f-rower/Crazyflie-monopod-perching/Results/TiltAngle.xlsx

Sheet: Sheet1
L | L/l | Theta | T1 | l | m | M | g
0.01 | 0.2857142857 | 30.14778759 | 0.05625 | 0.035 | 0.004 | 0.032 | 9.8 | 0.2857142857 | 32
0.02 | 0.5714285714 | 14.54356536 | 0.05625 | 0.035 | 0.004 | 0.032 | 9.8 | 0.5714285714 | 14.3
0.03 | 0.8571428571 | 9.637306499 | 0.05625 | 0.035 | 0.004 | 0.032 | 9.8 | 0.8571428571 | 12.2
0.04 | 1.142857143 | 7.212982772 | 0.05625 | 0.035 | 0.004 | 0.032 | 9.8 | 1.142857143 | 9.1
0.05 | 1.428571429 | 5.76487839 | 0.05625 | 0.035 | 0.004 | 0.032 | 9.8 | 1.714285714 | 6.9
0.06 | 1.714285714 | 4.801581975 | 0.05625 | 0.035 | 0.004 | 0.032 | 9.8 | 2.285714286 | 6.1
0.07 | 2 | 4.114361093 | 0.05625 | 0.035 | 0.004 | 0.032 | 9.8 | 2.857142857 | 4.33
0.08 | 2.285714286 | 3.5993397 | 0.05625 | 0.035 | 0.004 | 0.032 | 9.8 | 3.428571429 | 3.9
0.09 | 2.571428571 | 3.198970878 | 0.05625 | 0.035 | 0.004 | 0.032 | 9.8
0.1 | 2.857142857 | 2.878789307 | 0.05625 | 0.035 | 0.004 | 0.032 | 9.8
0.11 | 3.142857143 | 2.616889927 | 0.05625 | 0.035 | 0.004 | 0.032 | 9.8
0.12 | 3.428571429 | 2.398682465 | 0.05625 | 0.035 | 0.004 | 0.032 | 9.8
0.13 | 3.714285714 | 2.214072695 | 0.05625 | 0.035 | 0.004 | 0.032 | 9.8 |  | 0.01
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
