f-rower/Crazyflie-monopod-perching/Results/Pictures/1cm_oscillations.png

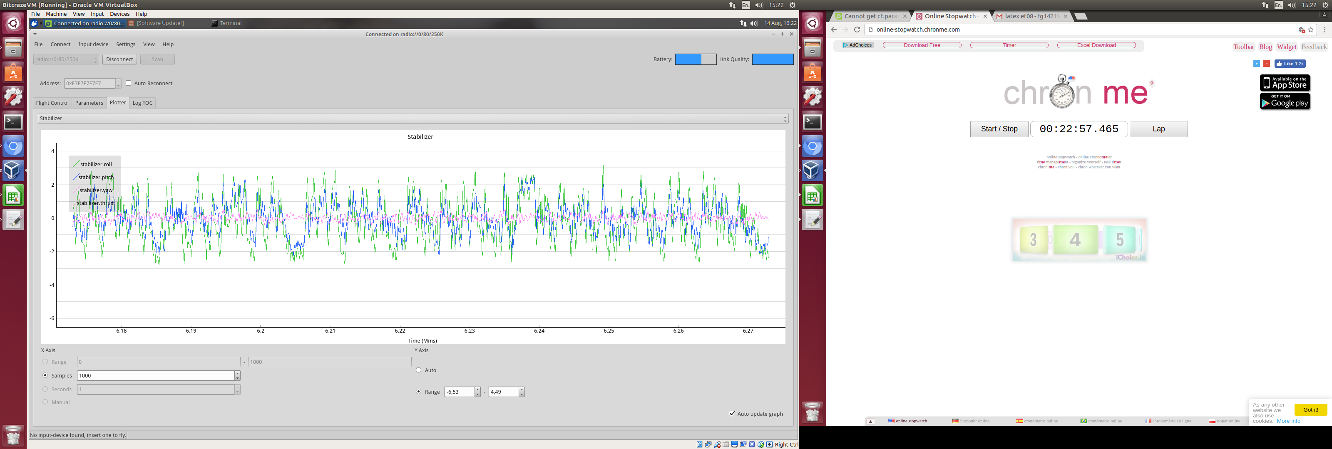
Results/Pictures/1cm_oscillations.png
