f-rower/Crazyflie-monopod-perching/Results/Pictures/2_cm_yellow_support_normal_battery.png

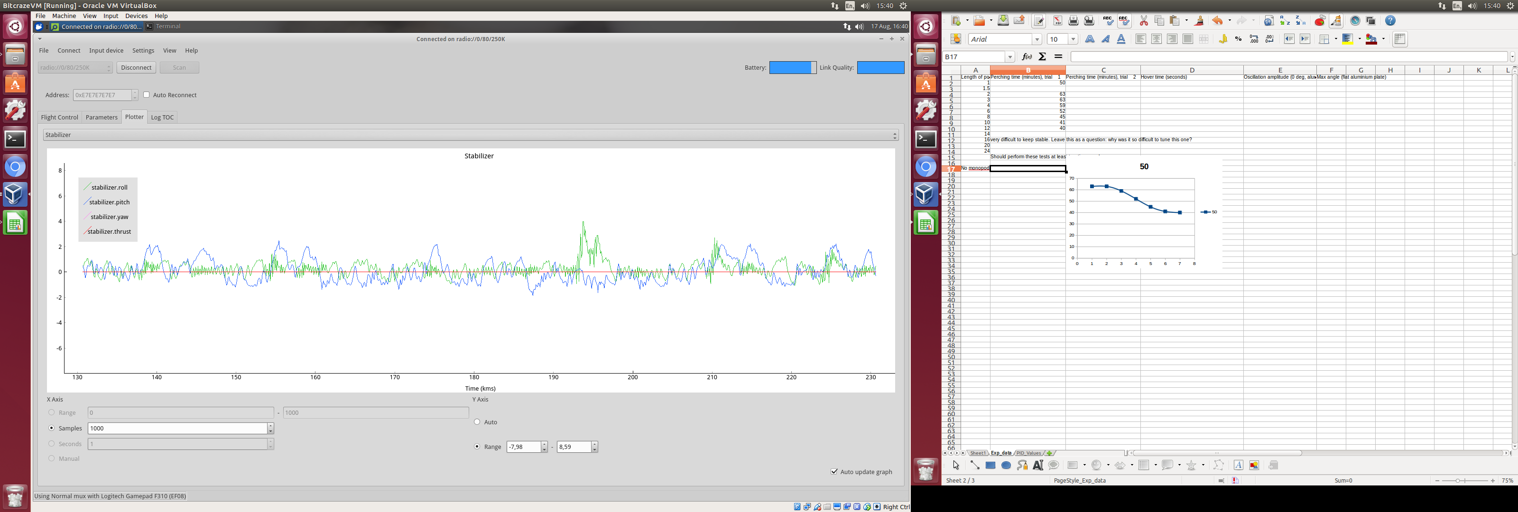
Results/Pictures/2_cm_yellow_support_normal_battery.png
