f-rower/Crazyflie-monopod-perching/Results/Pictures/2cm_pitch_1.png

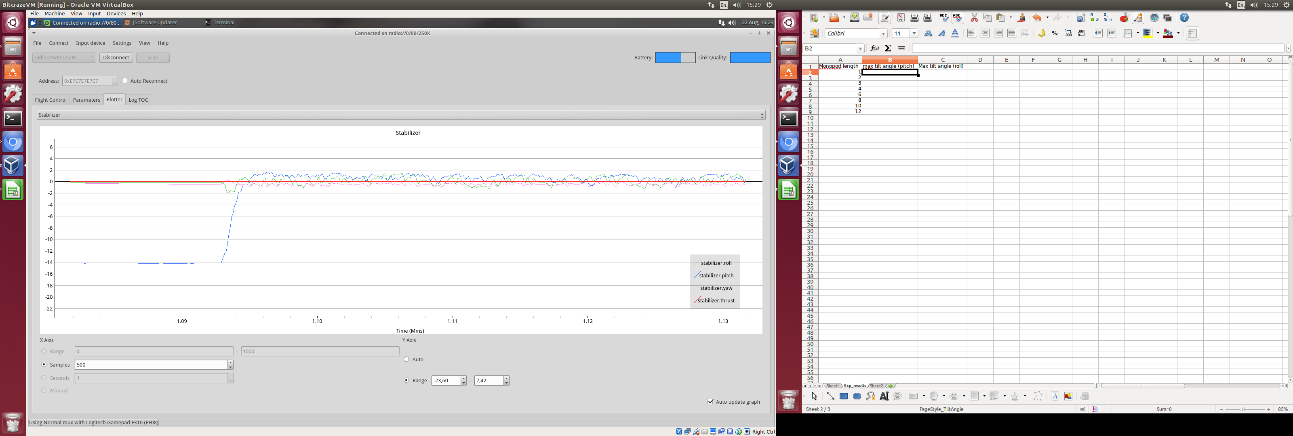
Results/Pictures/2cm_pitch_1.png
