f-rower/Crazyflie-monopod-perching/Results/Pictures/2cm_pitch_2.png

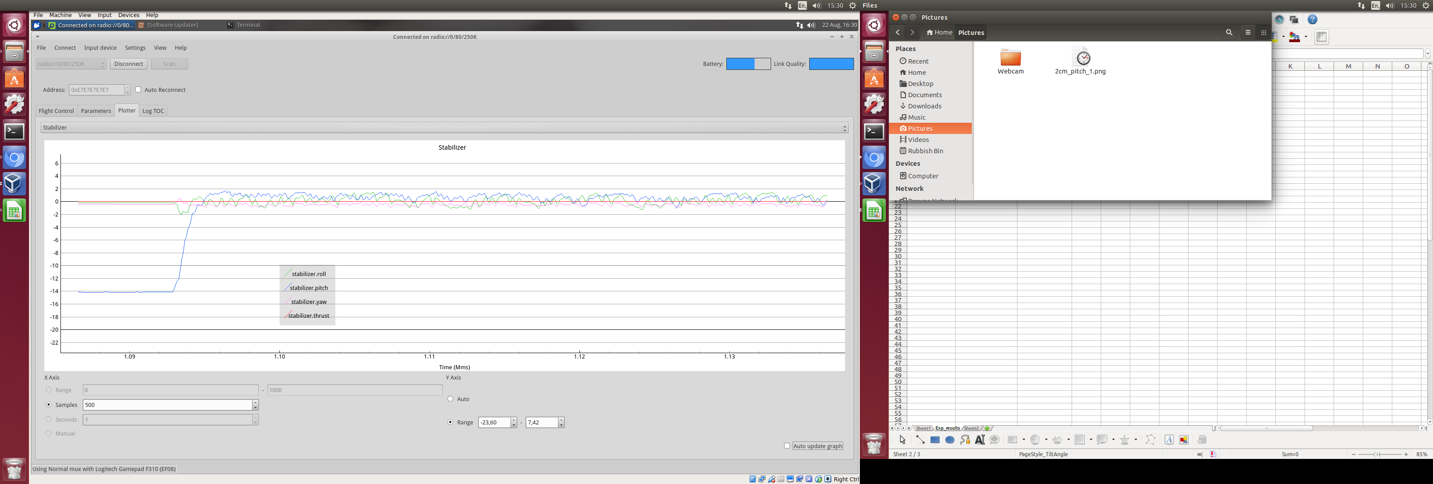
Results/Pictures/2cm_pitch_2.png
