f-rower/Crazyflie-monopod-perching/Results/Pictures/2cm_pitch_3.png

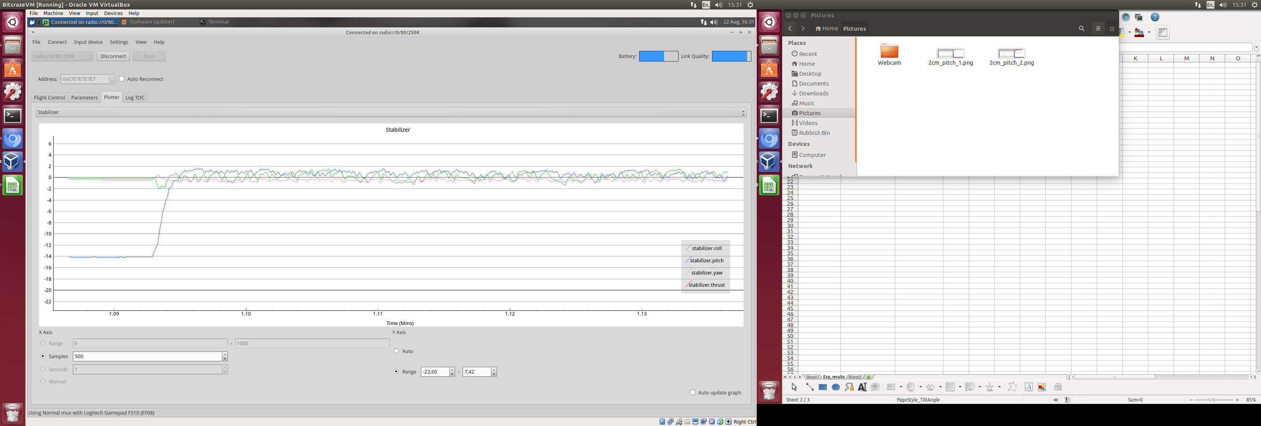
Results/Pictures/2cm_pitch_3.png
