f-rower/Crazyflie-monopod-perching/Results/Pictures/2cm_yawrate_2.png

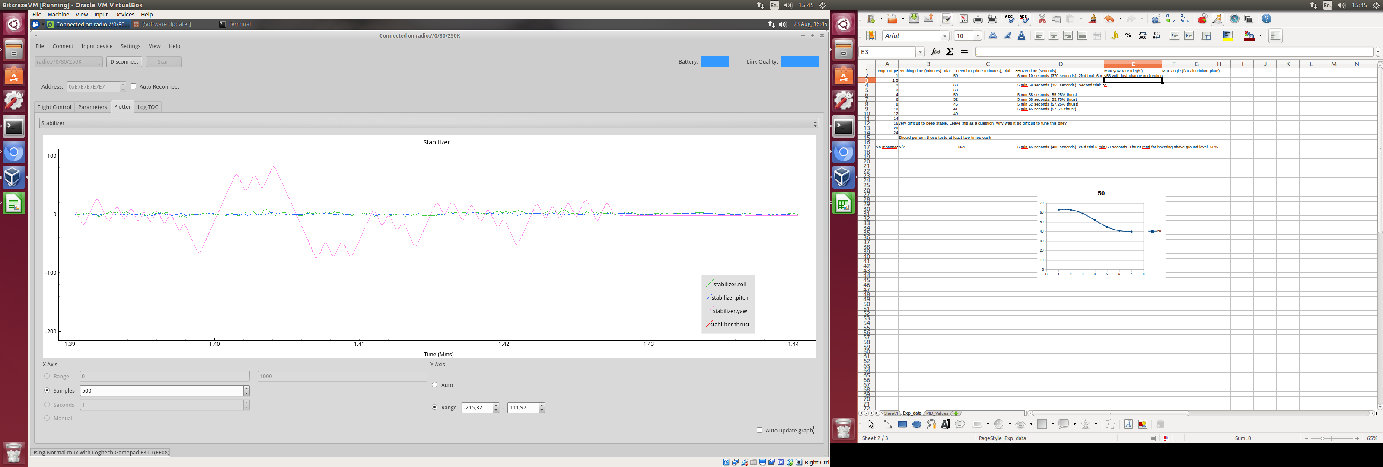
Results/Pictures/2cm_yawrate_2.png
