f-rower/Crazyflie-monopod-perching/Results/Pictures/4cm_pitch.png

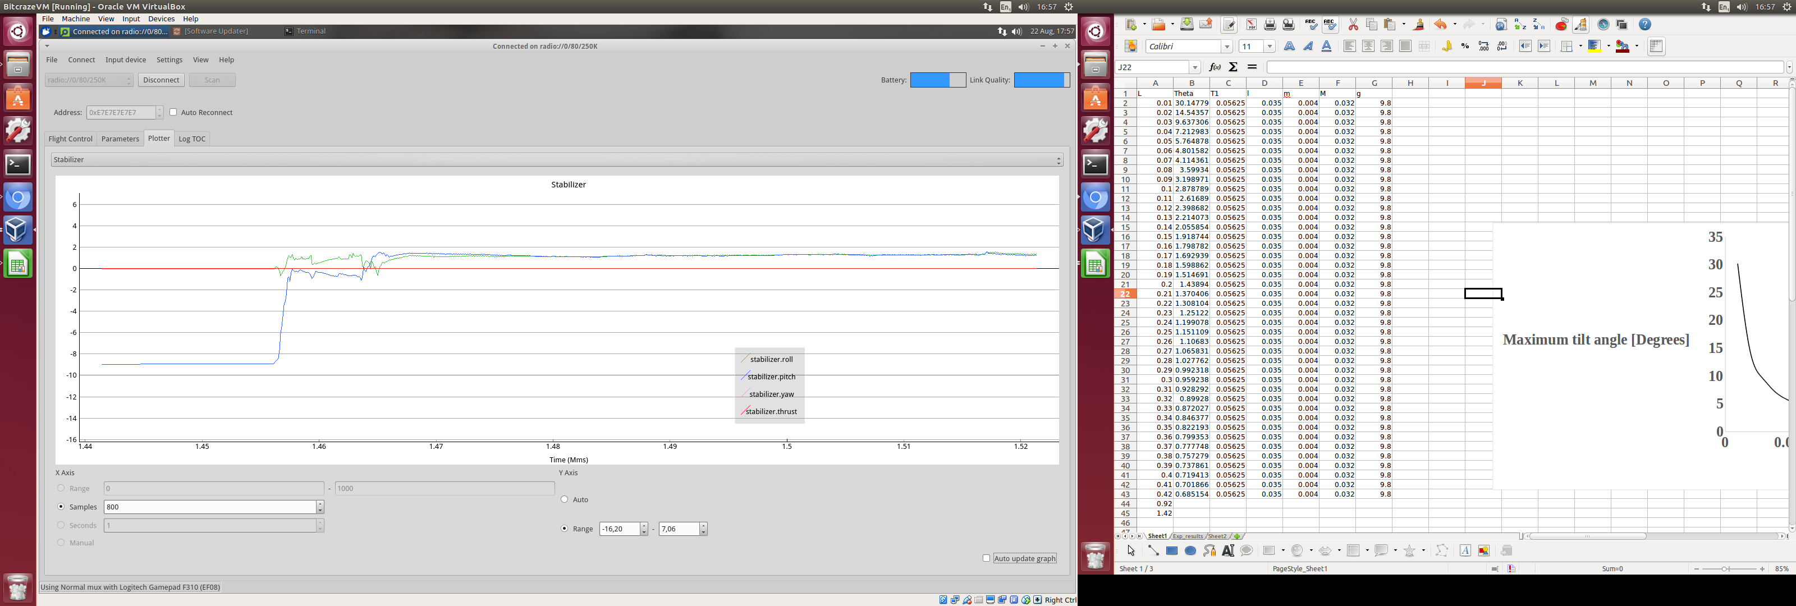
Results/Pictures/4cm_pitch.png
