f-rower/Crazyflie-monopod-perching/Results/Pictures/25_percent_base_thrust.png

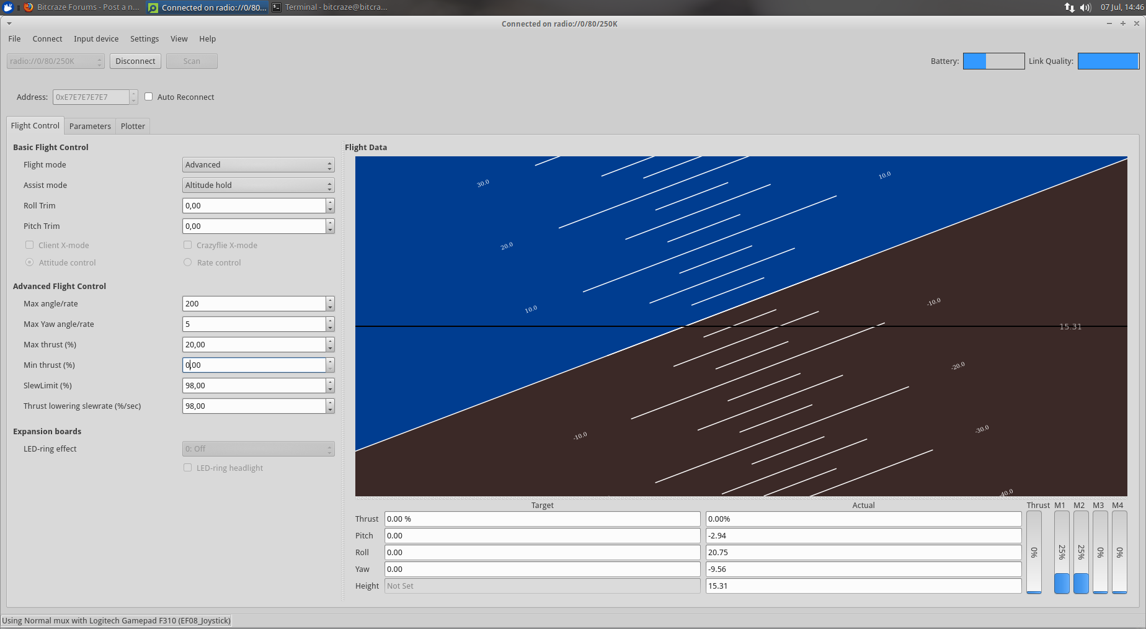
Results/Pictures/25_percent_base_thrust.png
