f-rower/Crazyflie-monopod-perching/Results/Pictures/457_goes_crazy.png

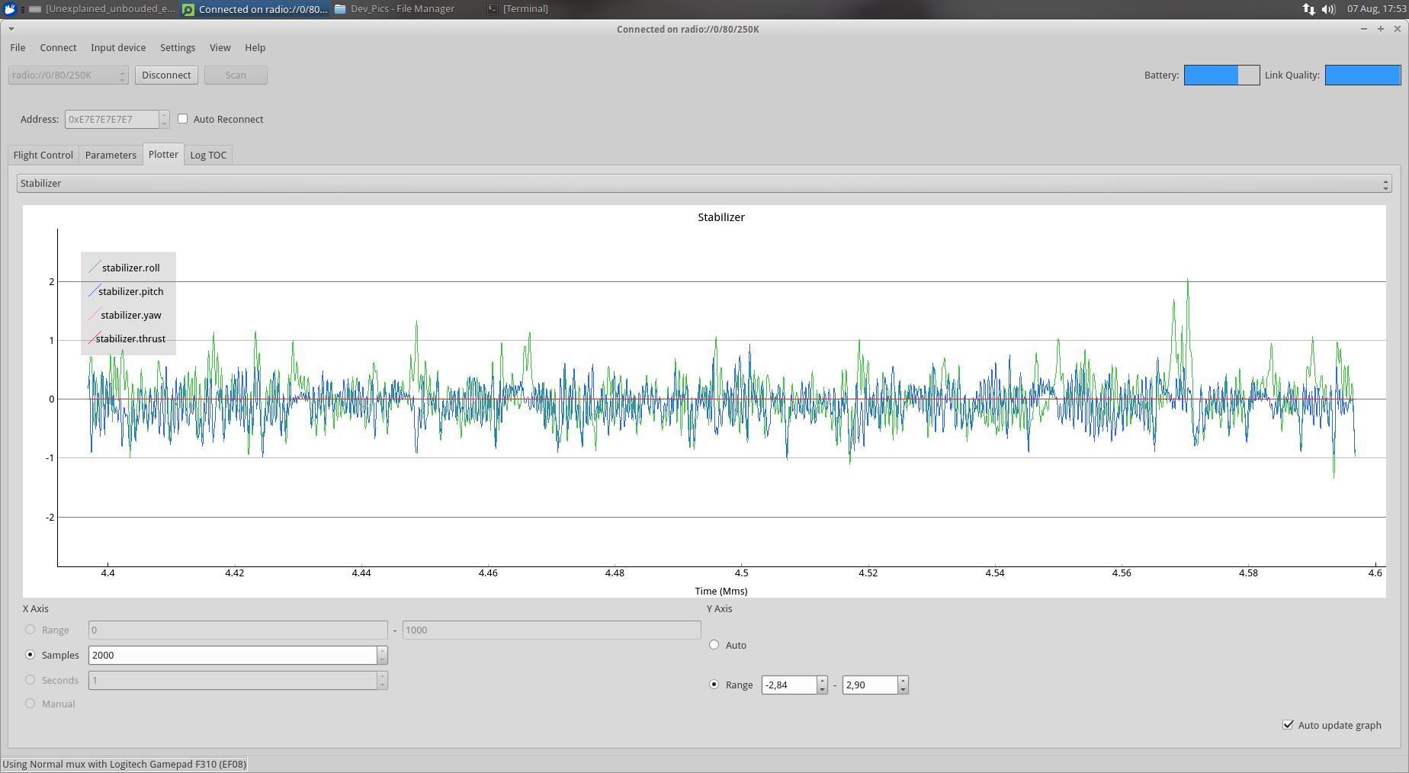
Results/Pictures/457_goes_crazy.png
