f-rower/Crazyflie-monopod-perching/Results/Pictures/2017_08_25/IMG_20170810_175333.jpg

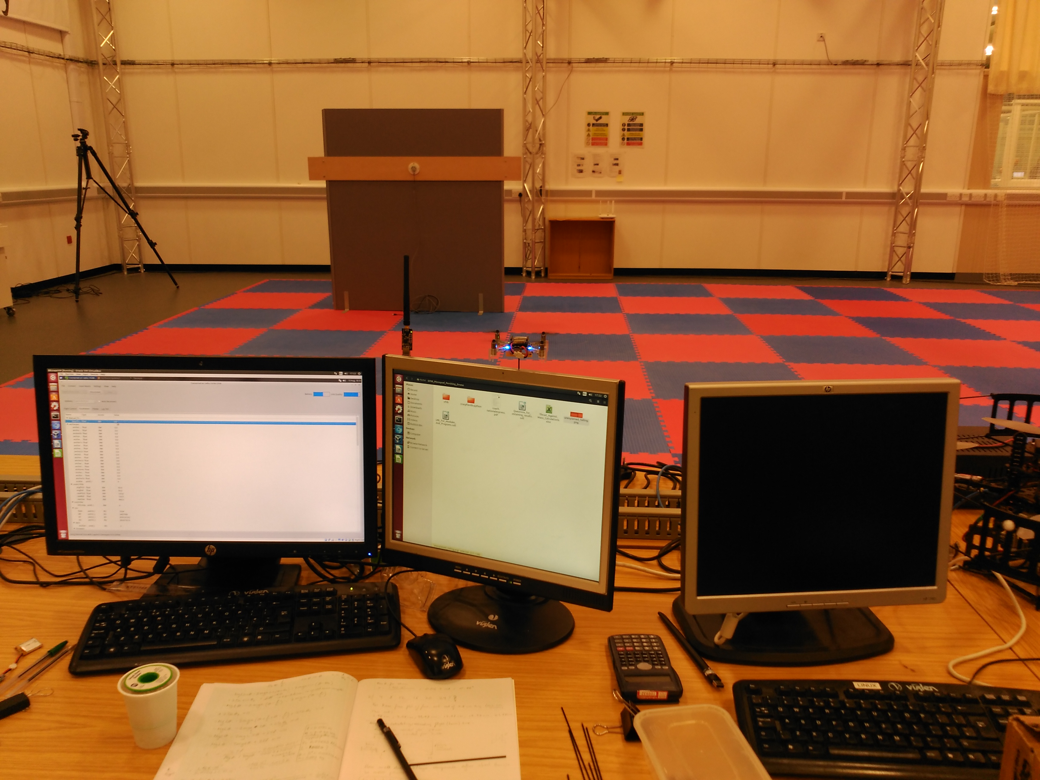
Results/Pictures/2017_08_25/IMG_20170810_175333.jpg
