f-rower/Crazyflie-monopod-perching/Results/Pictures/2017_08_25/IMG_20170825_134307.jpg

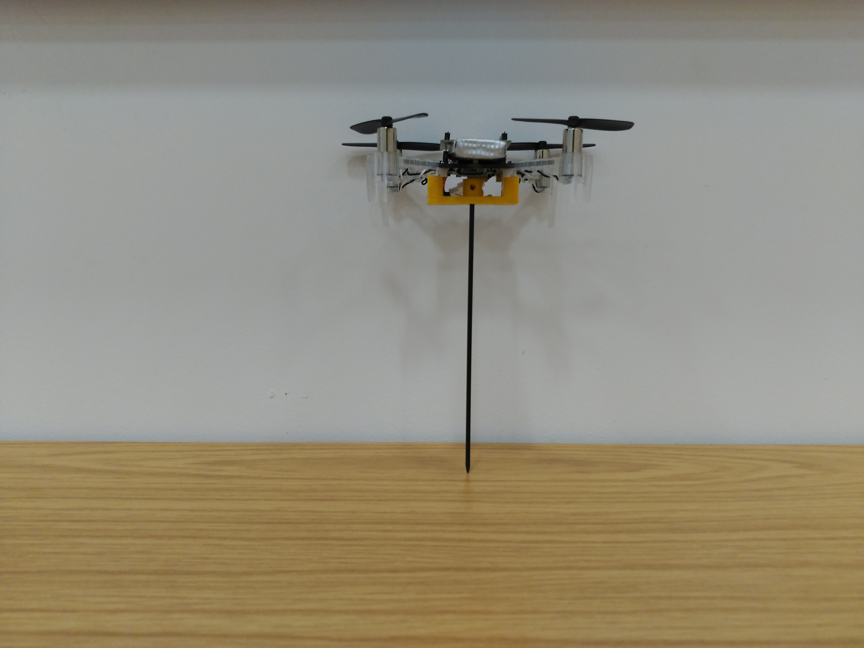
Results/Pictures/2017_08_25/IMG_20170825_134307.jpg
