f-rower/Crazyflie-monopod-perching/Results/Pictures/behaviour_when_low_battery.png

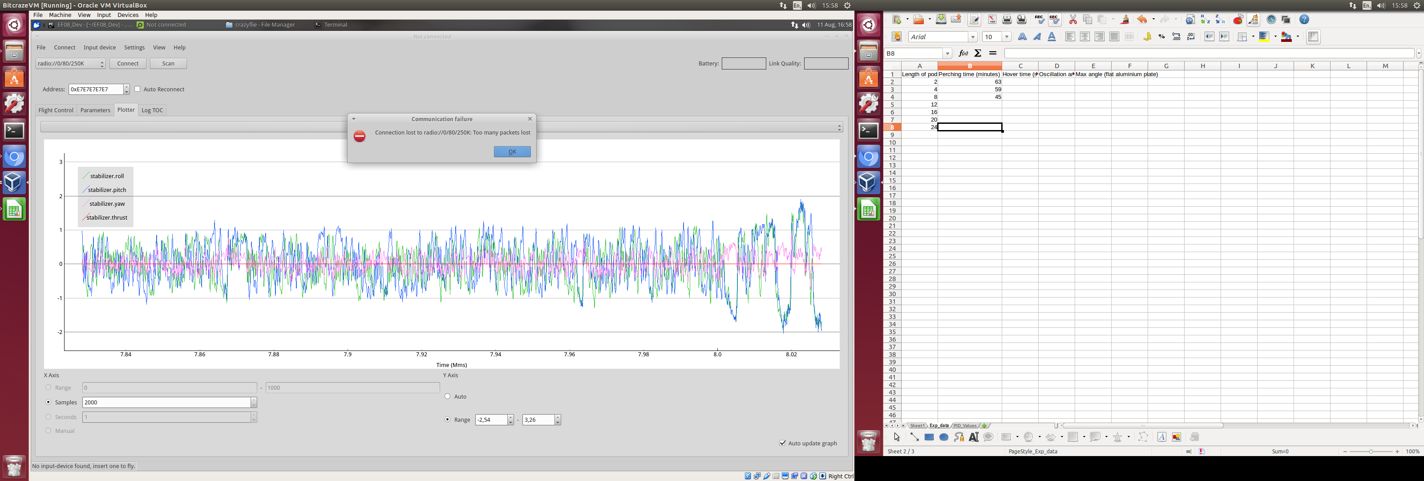
Results/Pictures/behaviour_when_low_battery.png
