f-rower/Crazyflie-monopod-perching/Results/Pictures/Motor_Voltage_end.png

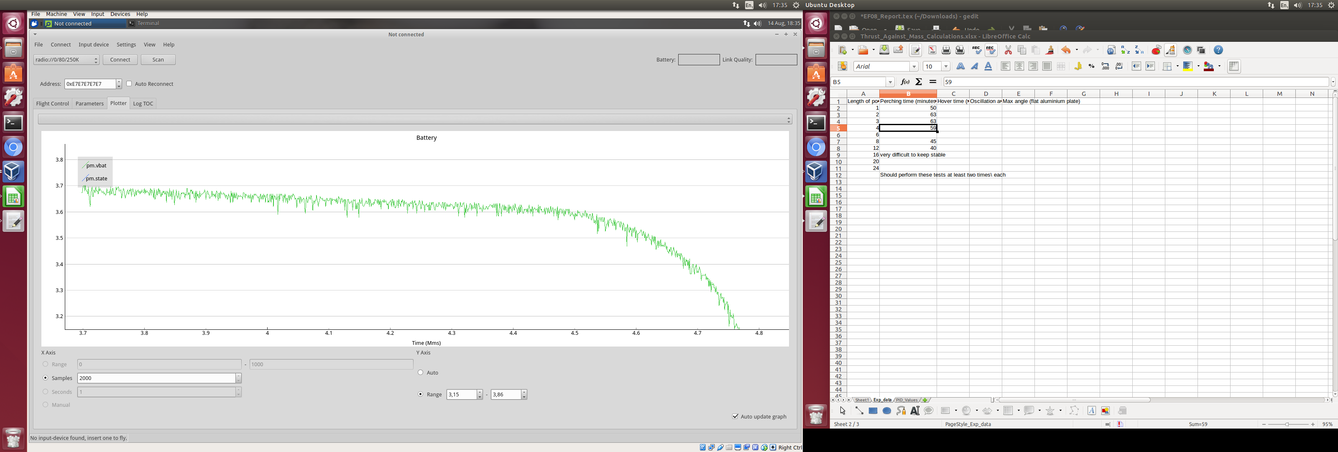
Results/Pictures/Motor_Voltage_end.png
