f-rower/Crazyflie-monopod-perching/Results/Pictures/Roll_1dof_rig_ratemode.png

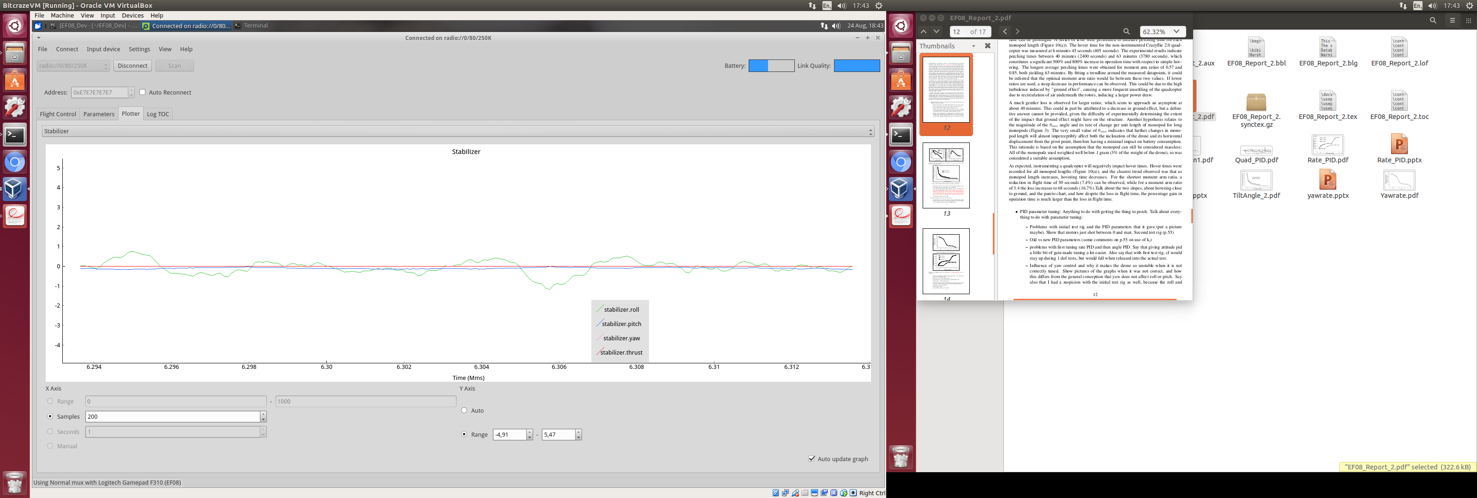
Results/Pictures/Roll_1dof_rig_ratemode.png
