f-rower/Crazyflie-monopod-perching/Results/Pictures/ROll_instability.png

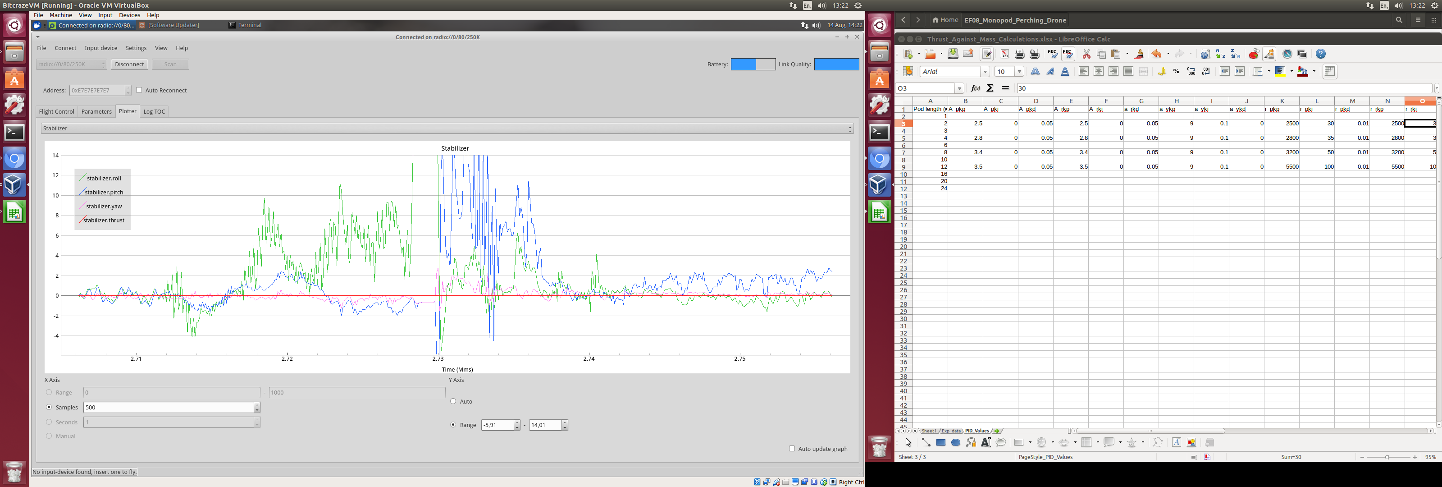
Results/Pictures/ROll_instability.png
