f-rower/Crazyflie-monopod-perching/Results/Pictures/Roll_Instability_2.png

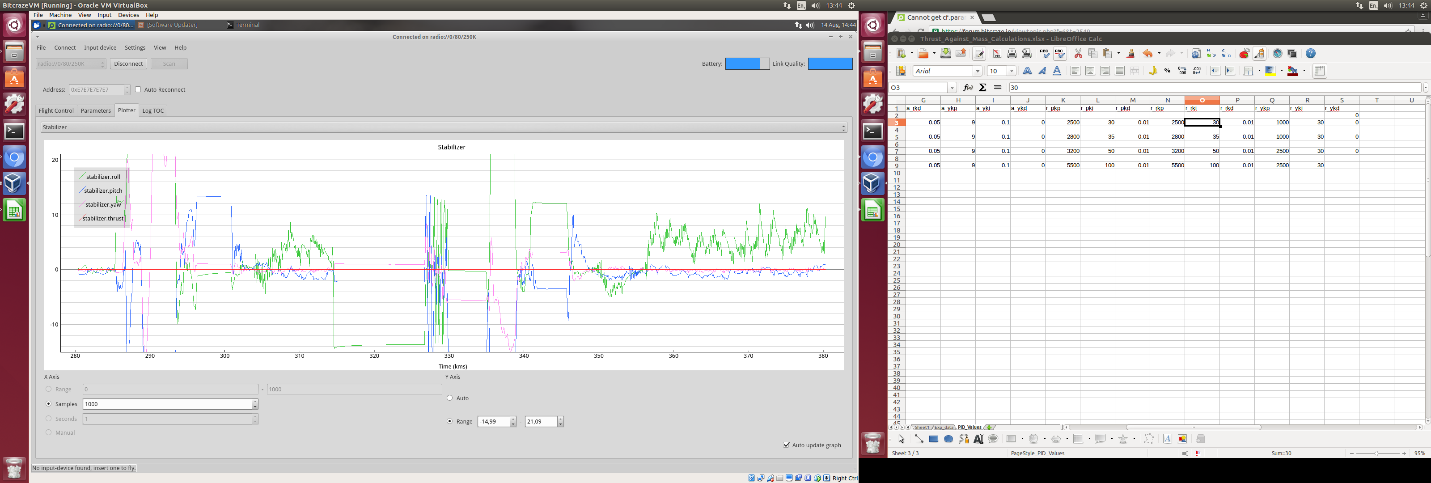
Results/Pictures/Roll_Instability_2.png
