f-rower/Crazyflie-monopod-perching/Results/Pictures/unexplained_falling.png

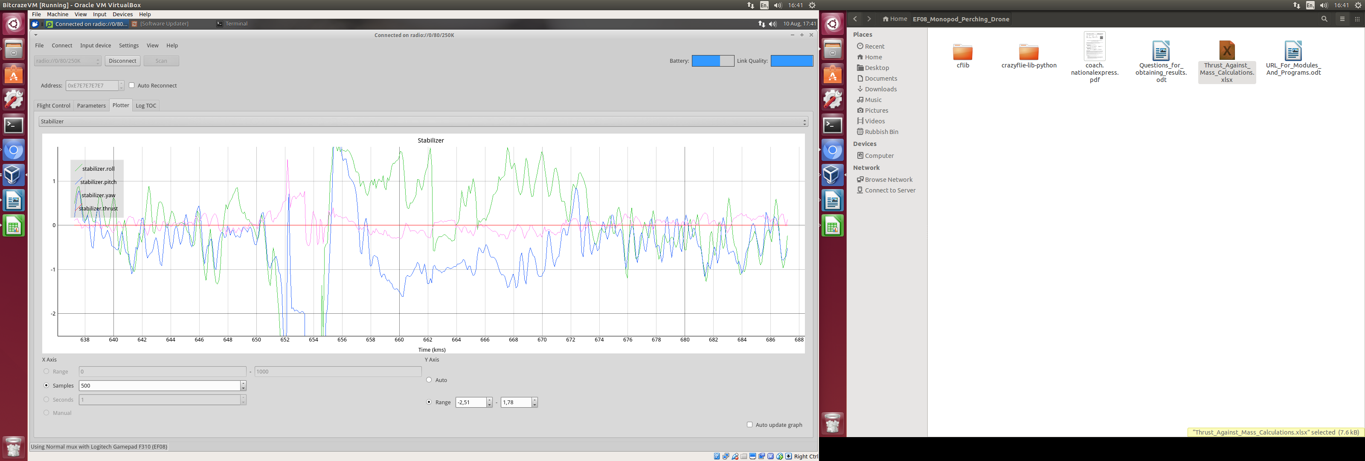
Results/Pictures/unexplained_falling.png
