f-rower/Crazyflie-monopod-perching/Results/Pictures/Unexplained_unbouded_error_growth-5.png

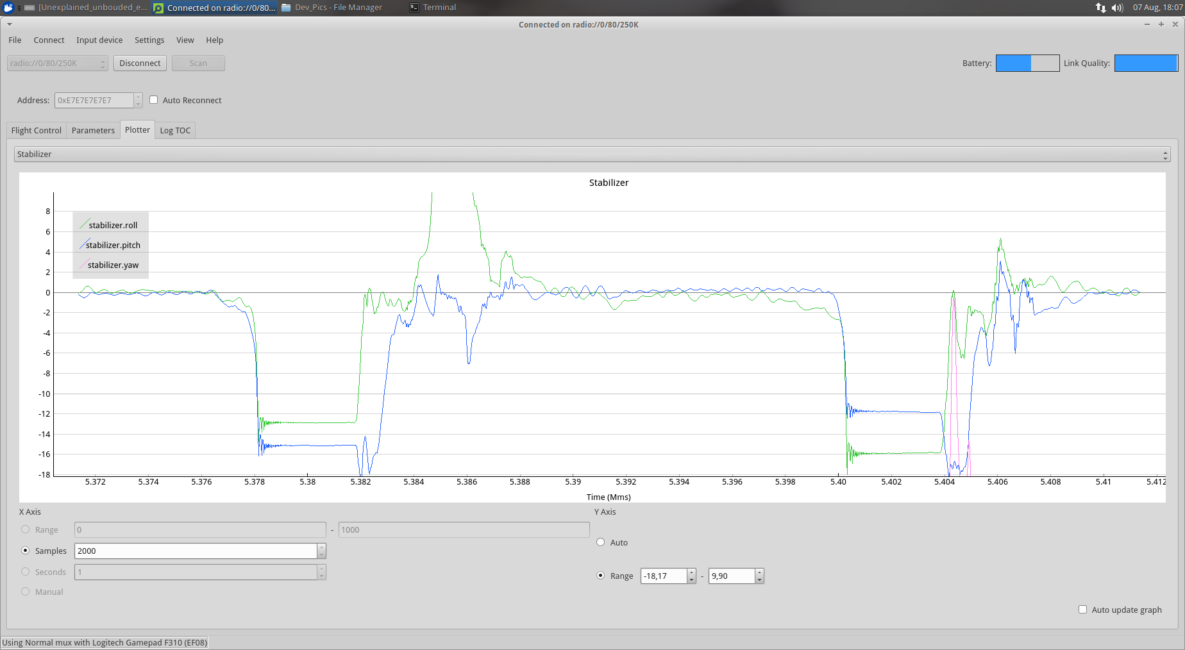
Results/Pictures/Unexplained_unbouded_error_growth-5.png
