f-rower/Crazyflie-monopod-perching/Results/Pictures/Unexplained_unbouded_error_growth.png

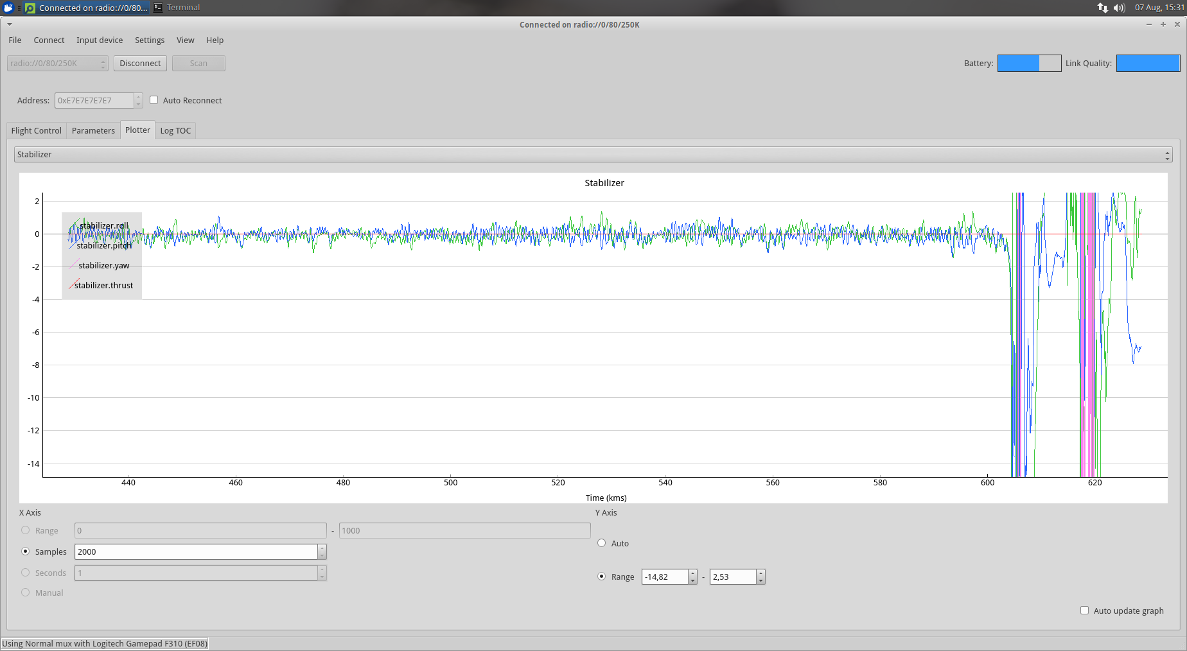
Results/Pictures/Unexplained_unbouded_error_growth.png
