f-rower/Crazyflie-monopod-perching/Results/Pictures/yaw_abnormal_behaviour.png

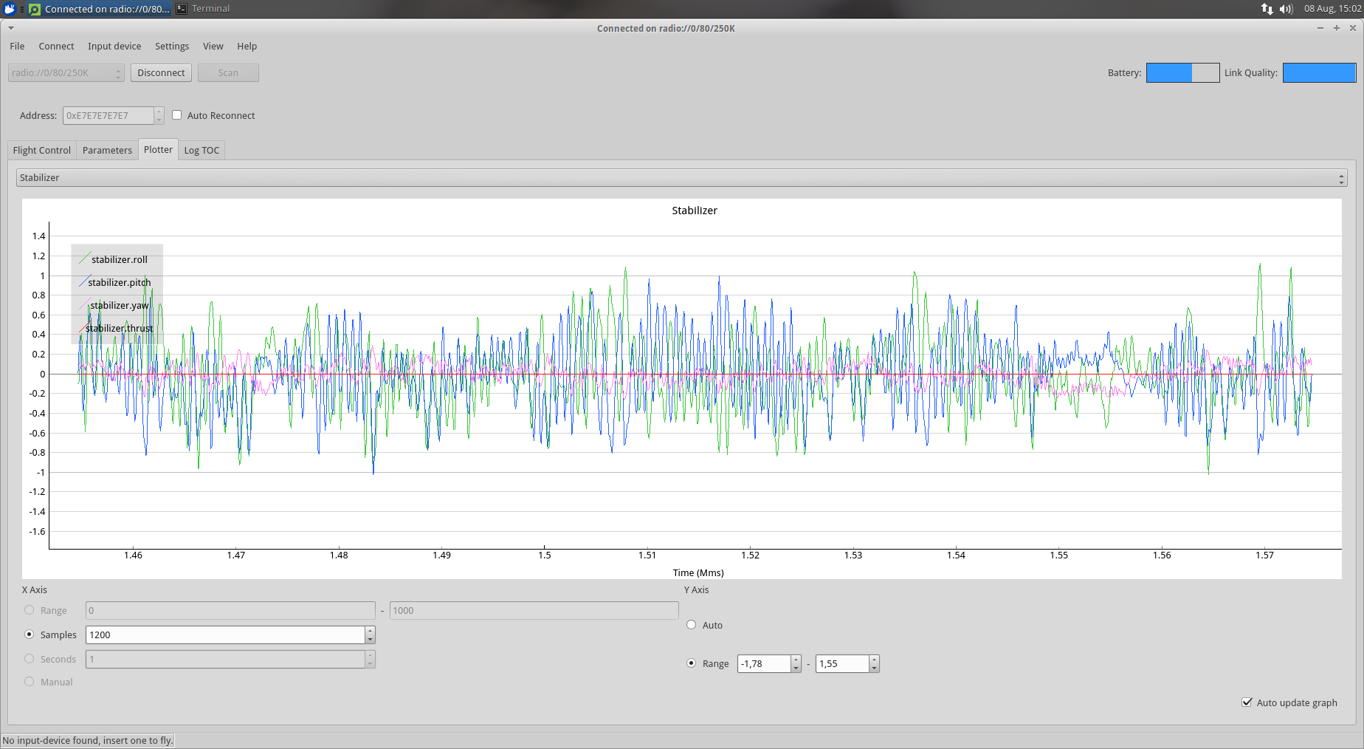
Results/Pictures/yaw_abnormal_behaviour.png
