f-rower/Crazyflie-monopod-perching/Results/Pictures/Yaw_error_growth.png

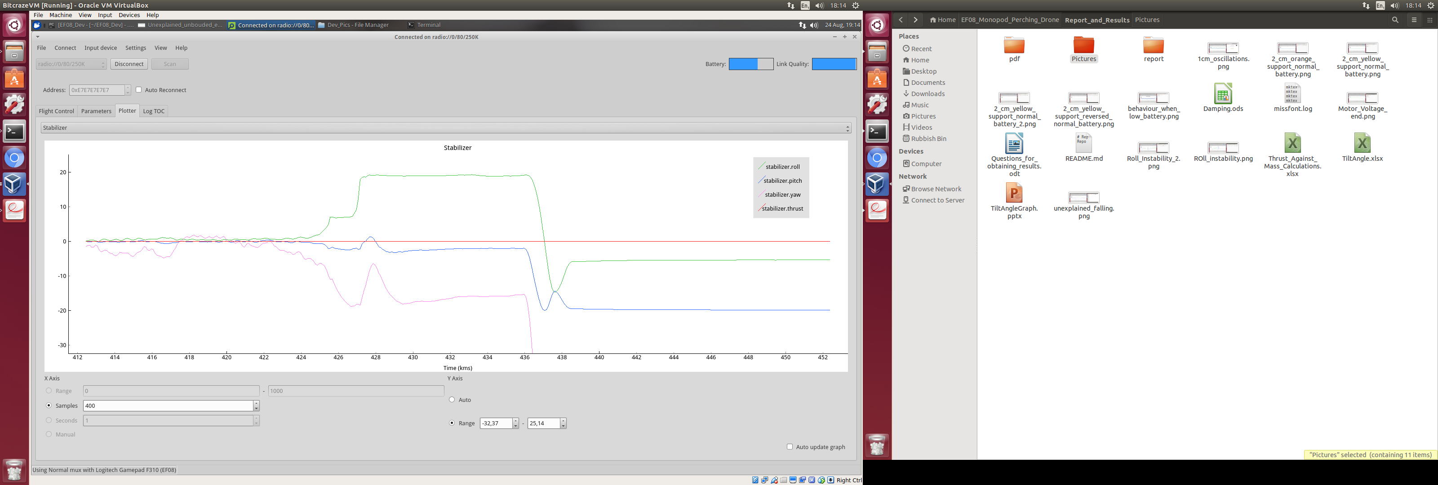
Results/Pictures/Yaw_error_growth.png
